leslier7/AirQualityPCB/Firmware/include/globals.h

// Robbie Leslie
// 2026

#ifndef GLOBALS_H
#define GLOBALS_H

#include <Arduino.h>

extern String FIRMWARE_VERSION;
extern const int FIRMWARE_VERSION_MAJOR;
extern const int FIRMWARE_VERSION_MINOR;
extern const int FIRMWARE_VERSION_PATCH ;

extern uint8_t device_id;

extern String server_name;

#endif
